mattybrad/polymod2/polymod_main/PhysicalControl.h

#ifndef PhysicalControl_h
#define PhysicalControl_h
#include "Arduino.h"

// Represents a real, physical analog control, such as a potentiometer

class PhysicalControl {
  public:
    PhysicalControl();
    bool active = false;
  private:

};

#endif
