mattybrad/polymod2/experiments/polymodnano/fakeserialmain/fakeserialmain.ino

#include <Wire.h>
bool ledStatus = false;
bool testMode = true;

void setup()
{
  pinMode(13, OUTPUT);
  if(testMode) Serial.begin(9600);
  else Serial.begin(31250);
  if(testMode) Serial.println("polymod main board started");
  Wire.begin(); // join i2c bus (address optional for master)
}

byte numDevicesTemp = 2;
byte tickNum = 0;
byte tempMsg[4][4]; // could reduce this to 3 because we know the module number

void loop()
{
  
  Wire.beginTransmission(0); // broadcast to all devices
  Wire.write(0); // message type 0 (tick)
  Wire.write(tickNum);
  Wire.endTransmission();    // stop transmitting
  /*Wire.beginTransmission(2); // broadcast to all devices
  Wire.write(0); // message type 0 (tick)
  Wire.write(tickNum);
  Wire.endTransmission();    // stop transmitting*/
  tickNum++;

  if(tickNum == 32) {
    for(byte n=1; n<=numDevicesTemp; n++) {
      Wire.requestFrom(n,18);
      byte x = 0;
      byte numNewConnected = 0;
      byte numNewDisconnected = 0;
      while(Wire.available()) {
        if(x==0) numNewConnected = Wire.read();
        else if(x==1) numNewDisconnected = Wire.read();
        else tempMsg[(x-2)/4][(x-2)%4] = Wire.read();
        x++;
      }
      for(byte i=0; i<numNewConnected + numNewDisconnected; i++) {
        if(testMode) {
          if(i<numNewConnected) Serial.print("connected ");
          else Serial.print("disconnected ");
          Serial.print(tempMsg[i][0], DEC);
          Serial.print(":");
          Serial.print(tempMsg[i][1], DEC);
          Serial.print(" to ");
          Serial.print(tempMsg[i][2], DEC);
          Serial.print(":");
          Serial.print(tempMsg[i][3], DEC);
          Serial.println("");
        } else {
          Serial.write(B11110000); // start sysex message
          Serial.write(0x7D); // temporary manufacturer ID
          if(i<numNewConnected) {
            Serial.write(2); // connected
          } else {
            Serial.write(3); // disconnected
          }
          Serial.write(tempMsg[i][0]);
          Serial.write(tempMsg[i][1]);
          Serial.write(tempMsg[i][2]);
          Serial.write(tempMsg[i][3]);
          Serial.write(B11110111); // end message
        }
      }
    }
    tickNum = 0;
    delayMicroseconds(100);
  }

  delayMicroseconds(100);
}
